ThorstenBr/FloppyEmuDiskIIEnclosure/sticker/HighQuality/BackLabel_Style2/FEMU Back Label GERMANY REV-1 - 000001.pdf

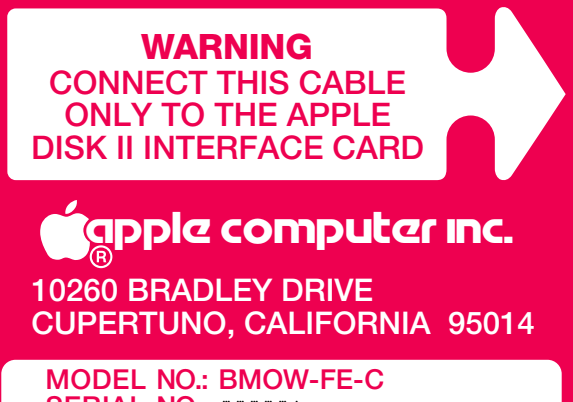
[picture p24: figure]
MODEL; WARNING CONNECT THIS CABLE ONLY TO THE APPLE DISK II INTERFACE CARD; 10260 BRADLEY DRIVE CUPERTUNO, CALIFORNIA 95014; apple computerinc.; BMOW-FE-C

NO.:

SERIAL 000001
- MADE IN GERMANY
