ThorstenBr/FloppyEmuDiskIIEnclosure/resources/Stickers1.jpg

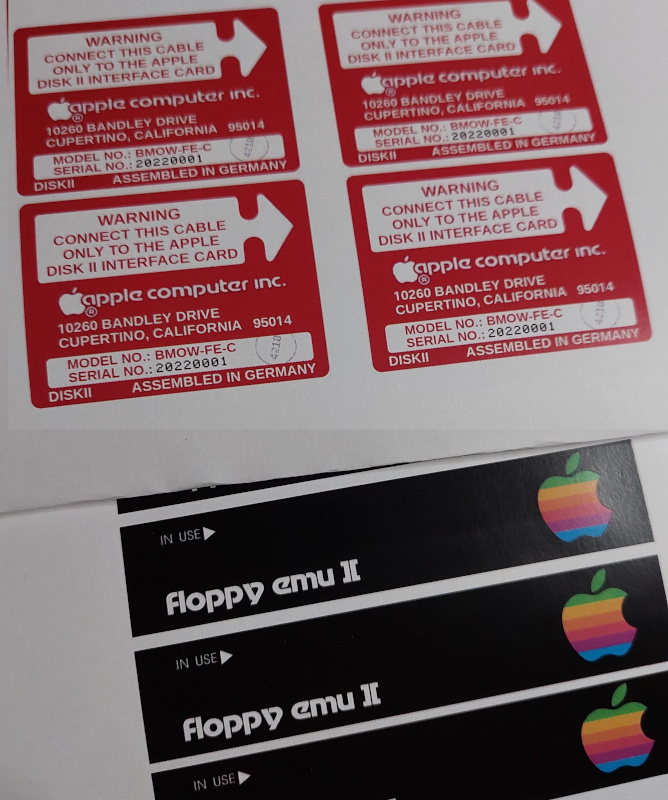
resources/Stickers1.jpg
