ThorstenBr/FloppyEmuDiskIIEnclosure/resources/Stickers2.jpg

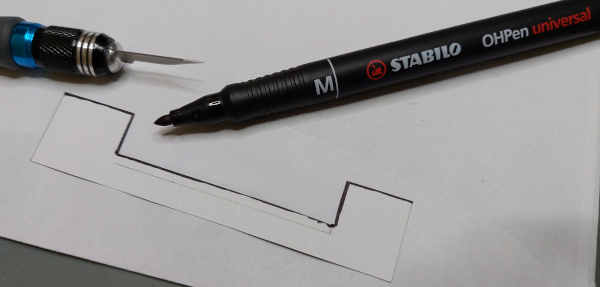
resources/Stickers2.jpg
