ThorstenBr/FloppyEmuDiskIIEnclosure/sticker/FrontPanel.png

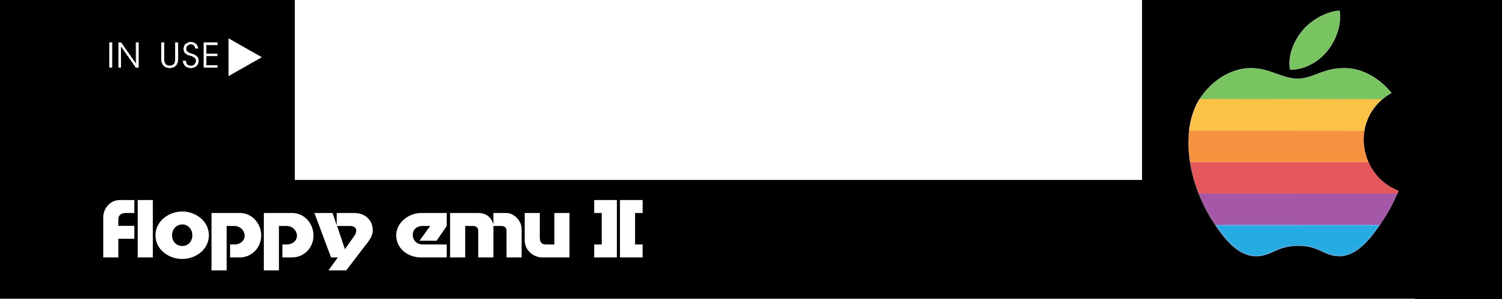
sticker/FrontPanel.png
