ThorstenBr/FloppyEmuDiskIIEnclosure/sticker/HighQuality/FrontLabel/DISK II Front Panel Rev-1.jpg

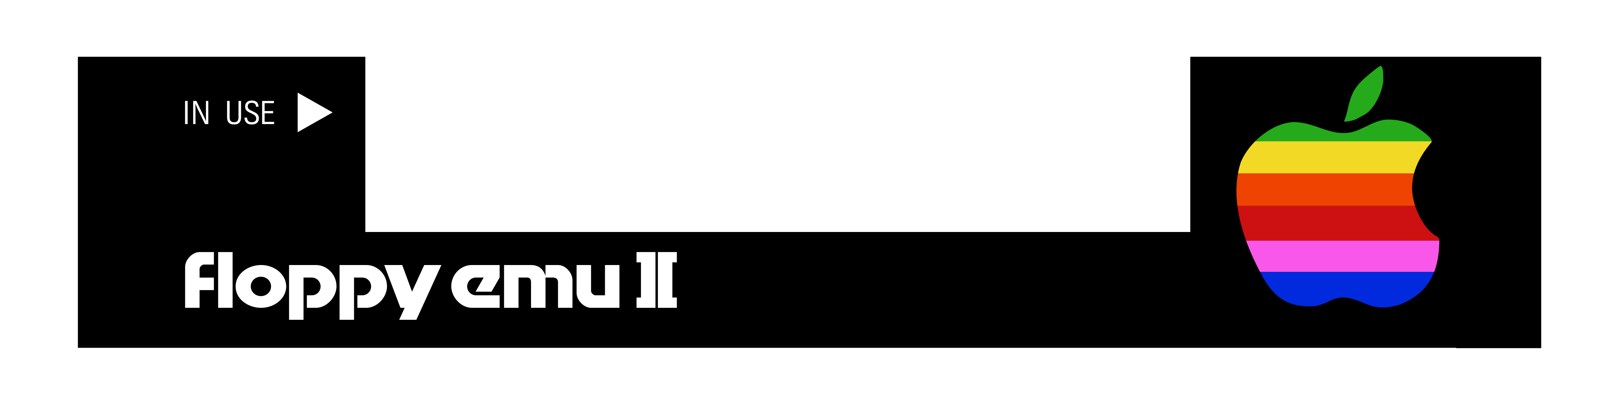
sticker/HighQuality/FrontLabel/DISK II Front Panel Rev-1.jpg
